psx360/meeting-assistant/hardware/kicad/meeting-assistant.kicad_sch

## KiCad design hardware/kicad/meeting-assistant.kicad_sch (2026-09-02)

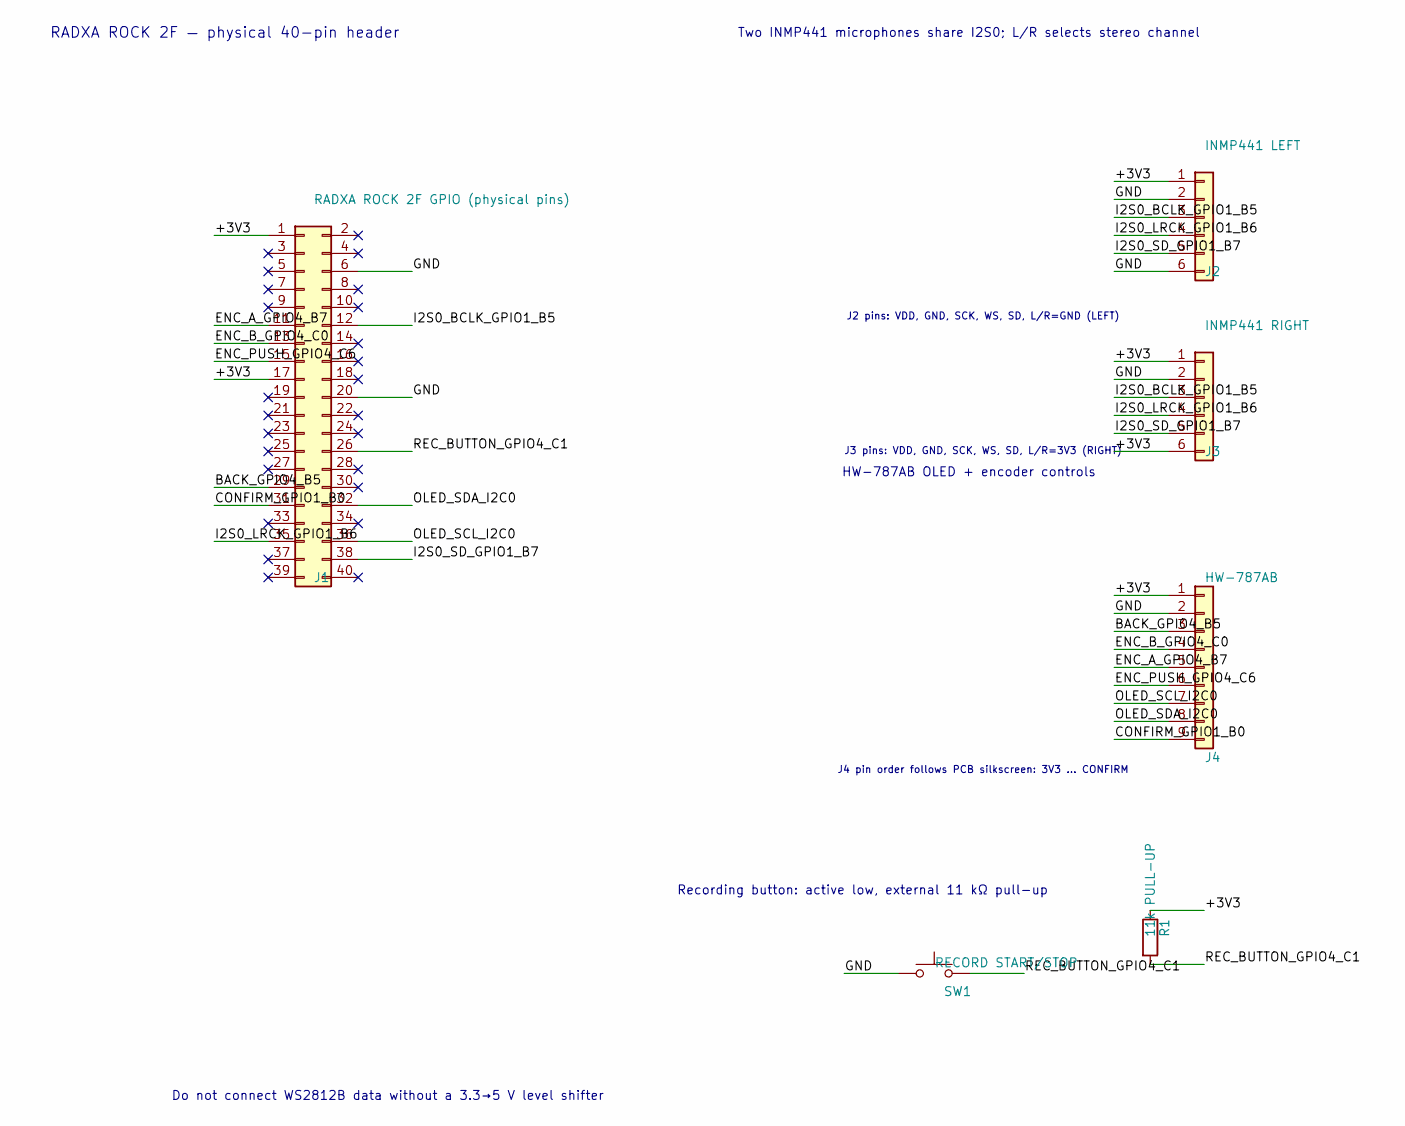
[picture p3: schematic meeting-assistant.kicad_sch]

Parts:
J1: RADXA ROCK 2F GPIO (physical pins)
J2: INMP441 LEFT
J3: INMP441 RIGHT
J4: HW-787AB
R1: 11k PULL-UP
SW1: RECORD START/STOP

Connections:
+3V3: J1.1, J1.17, J2.1, J3.1, J3.6, J4.1, R1.1
BACK_GPIO4_B5: J1.29, J4.3
CONFIRM_GPIO1_B0: J1.31, J4.9
ENC_A_GPIO4_B7: J1.11, J4.5
ENC_B_GPIO4_C0: J1.13, J4.4
ENC_PUSH_GPIO4_C6: J1.15, J4.6
GND: J1.6, J1.20, J2.2, J2.6, J3.2, J4.2, SW1.1
I2S0_BCLK_GPIO1_B5: J1.12, J2.3, J3.3
I2S0_LRCK_GPIO1_B6: J1.35, J2.4, J3.4
I2S0_SD_GPIO1_B7: J1.38, J2.5, J3.5
OLED_SCL_I2C0: J1.36, J4.7
OLED_SDA_I2C0: J1.32, J4.8
REC_BUTTON_GPIO4_C1: J1.26, R1.2, SW1.2

Notes on the sheet:
RADXA ROCK 2F — physical 40-pin header
Two INMP441 microphones share I2S0; L/R selects stereo channel
HW-787AB OLED + encoder controls
Recording button: active low, external 11 kΩ pull-up
J2 pins: VDD, GND, SCK, WS, SD, L/R=GND (LEFT)
J3 pins: VDD, GND, SCK, WS, SD, L/R=3V3 (RIGHT)
J4 pin order follows PCB silkscreen: 3V3 … CONFIRM
Do not connect WS2812B data without a 3.3→5 V level shifter
