psx360/meeting-assistant/meeting-documents.py

#!/usr/bin/python3
"""Small dependency-free DOCX builder for meeting-assistant deliveries."""

import io
import re
import zipfile
from datetime import datetime, timezone
from xml.sax.saxutils import escape


CONTENT_TYPES = """<?xml version="1.0" encoding="UTF-8" standalone="yes"?>
<Types xmlns="http://schemas.openxmlformats.org/package/2006/content-types">
  <Default Extension="rels" ContentType="application/vnd.openxmlformats-package.relationships+xml"/>
  <Default Extension="xml" ContentType="application/xml"/>
  <Override PartName="/word/document.xml" ContentType="application/vnd.openxmlformats-officedocument.wordprocessingml.document.main+xml"/>
  <Override PartName="/word/styles.xml" ContentType="application/vnd.openxmlformats-officedocument.wordprocessingml.styles+xml"/>
  <Override PartName="/docProps/core.xml" ContentType="application/vnd.openxmlformats-package.core-properties+xml"/>
  <Override PartName="/docProps/app.xml" ContentType="application/vnd.openxmlformats-officedocument.extended-properties+xml"/>
</Types>"""

ROOT_RELS = """<?xml version="1.0" encoding="UTF-8" standalone="yes"?>
<Relationships xmlns="http://schemas.openxmlformats.org/package/2006/relationships">
  <Relationship Id="rId1" Type="http://schemas.openxmlformats.org/officeDocument/2006/relationships/officeDocument" Target="word/document.xml"/>
  <Relationship Id="rId2" Type="http://schemas.openxmlformats.org/package/2006/relationships/metadata/core-properties" Target="docProps/core.xml"/>
  <Relationship Id="rId3" Type="http://schemas.openxmlformats.org/officeDocument/2006/relationships/extended-properties" Target="docProps/app.xml"/>
</Relationships>"""

DOCUMENT_RELS = """<?xml version="1.0" encoding="UTF-8" standalone="yes"?>
<Relationships xmlns="http://schemas.openxmlformats.org/package/2006/relationships">
  <Relationship Id="rId1" Type="http://schemas.openxmlformats.org/officeDocument/2006/relationships/styles" Target="styles.xml"/>
</Relationships>"""

# standard_business_brief: Letter, 1-inch margins, Calibri 11 pt, restrained blue headings.
STYLES = """<?xml version="1.0" encoding="UTF-8" standalone="yes"?>
<w:styles xmlns:w="http://schemas.openxmlformats.org/wordprocessingml/2006/main">
  <w:docDefaults><w:rPrDefault><w:rPr><w:rFonts w:ascii="Calibri" w:hAnsi="Calibri" w:eastAsia="Calibri"/><w:sz w:val="22"/><w:szCs w:val="22"/><w:lang w:val="ru-RU"/></w:rPr></w:rPrDefault></w:docDefaults>
  <w:style w:type="paragraph" w:default="1" w:styleId="Normal"><w:name w:val="Normal"/><w:pPr><w:spacing w:after="120" w:line="264" w:lineRule="auto"/></w:pPr></w:style>
  <w:style w:type="paragraph" w:styleId="Title"><w:name w:val="Title"/><w:basedOn w:val="Normal"/><w:next w:val="Normal"/><w:pPr><w:spacing w:after="240"/></w:pPr><w:rPr><w:b/><w:color w:val="1F4D78"/><w:sz w:val="36"/><w:szCs w:val="36"/></w:rPr></w:style>
  <w:style w:type="paragraph" w:styleId="Heading1"><w:name w:val="heading 1"/><w:basedOn w:val="Normal"/><w:next w:val="Normal"/><w:qFormat/><w:pPr><w:keepNext/><w:spacing w:before="320" w:after="160"/><w:outlineLvl w:val="0"/></w:pPr><w:rPr><w:b/><w:color w:val="2E74B5"/><w:sz w:val="32"/><w:szCs w:val="32"/></w:rPr></w:style>
  <w:style w:type="paragraph" w:styleId="Heading2"><w:name w:val="heading 2"/><w:basedOn w:val="Normal"/><w:next w:val="Normal"/><w:qFormat/><w:pPr><w:keepNext/><w:spacing w:before="240" w:after="120"/><w:outlineLvl w:val="1"/></w:pPr><w:rPr><w:b/><w:color w:val="2E74B5"/><w:sz w:val="26"/><w:szCs w:val="26"/></w:rPr></w:style>
</w:styles>"""


def _paragraph(text, style="Normal"):
    if not text:
        return "<w:p/>"
    preserved = ' xml:space="preserve"' if text[:1].isspace() or text[-1:].isspace() else ""
    return f'<w:p><w:pPr><w:pStyle w:val="{style}"/></w:pPr><w:r><w:t{preserved}>{escape(text)}</w:t></w:r></w:p>'


def _body_paragraphs(text, structured=False):
    paragraphs = []
    for raw in text.replace("\r\n", "\n").replace("\r", "\n").split("\n"):
        line = raw.strip()
        style = "Normal"
        if structured:
            match = re.match(r"^(#{1,2})\s+(.+)$", line)
            if match:
                line = match.group(2).strip()
                style = "Heading1" if len(match.group(1)) == 1 else "Heading2"
            elif re.match(r"^\d+[.)]\s+\S", line) and len(line) < 120:
                style = "Heading1"
        paragraphs.append(_paragraph(line, style))
    return "".join(paragraphs)


def build_docx(title, text, structured=False):
    now = datetime.now(timezone.utc).replace(microsecond=0).isoformat().replace("+00:00", "Z")
    document = f'''<?xml version="1.0" encoding="UTF-8" standalone="yes"?>
<w:document xmlns:w="http://schemas.openxmlformats.org/wordprocessingml/2006/main"><w:body>
{_paragraph(title, "Title")}{_body_paragraphs(text, structured)}
<w:sectPr><w:pgSz w:w="12240" w:h="15840"/><w:pgMar w:top="1440" w:right="1440" w:bottom="1440" w:left="1440" w:header="708" w:footer="708" w:gutter="0"/></w:sectPr>
</w:body></w:document>'''
    core = f'''<?xml version="1.0" encoding="UTF-8" standalone="yes"?>
<cp:coreProperties xmlns:cp="http://schemas.openxmlformats.org/package/2006/metadata/core-properties" xmlns:dc="http://purl.org/dc/elements/1.1/" xmlns:dcterms="http://purl.org/dc/terms/" xmlns:xsi="http://www.w3.org/2001/XMLSchema-instance"><dc:title>{escape(title)}</dc:title><dc:creator>Meeting Assistant</dc:creator><dcterms:created xsi:type="dcterms:W3CDTF">{now}</dcterms:created></cp:coreProperties>'''
    app = '''<?xml version="1.0" encoding="UTF-8" standalone="yes"?><Properties xmlns="http://schemas.openxmlformats.org/officeDocument/2006/extended-properties"><Application>Meeting Assistant</Application></Properties>'''
    output = io.BytesIO()
    with zipfile.ZipFile(output, "w", zipfile.ZIP_DEFLATED) as archive:
        archive.writestr("[Content_Types].xml", CONTENT_TYPES)
        archive.writestr("_rels/.rels", ROOT_RELS)
        archive.writestr("word/document.xml", document)
        archive.writestr("word/styles.xml", STYLES)
        archive.writestr("word/_rels/document.xml.rels", DOCUMENT_RELS)
        archive.writestr("docProps/core.xml", core)
        archive.writestr("docProps/app.xml", app)
    return output.getvalue()
